mgesteiro/escornabot-Brivoi-DIY/3D/escornabot_back.png

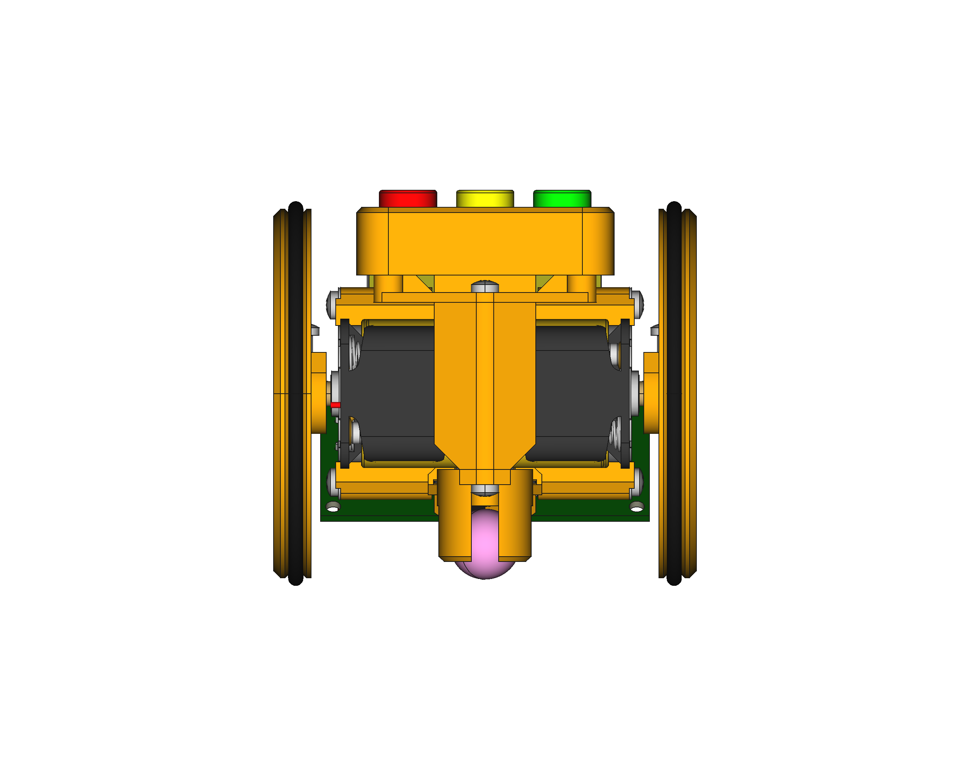
3D/escornabot_back.png
