mgesteiro/escornabot-Brivoi-DIY/3D/escornabot_bottom.png

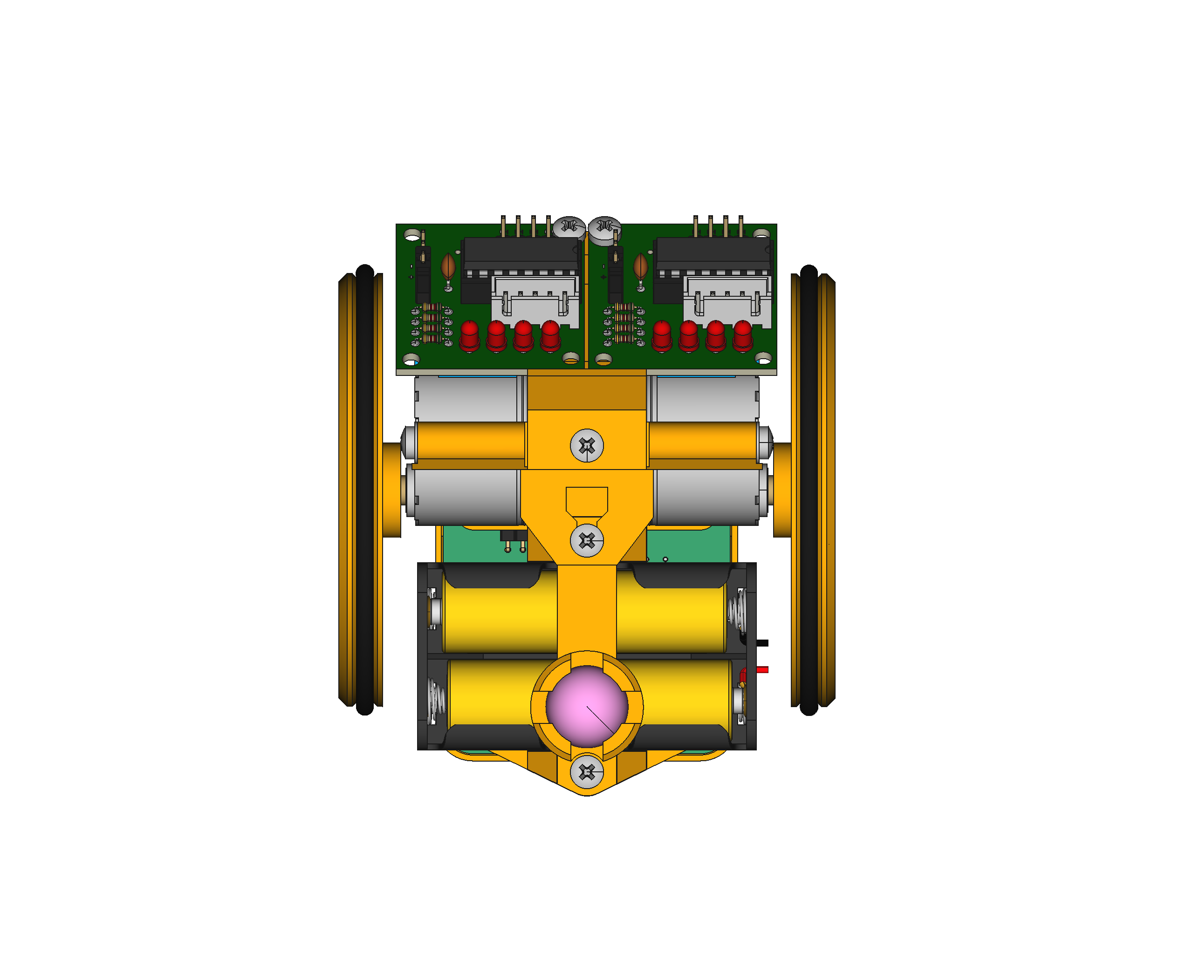
3D/escornabot_bottom.png
