mgesteiro/escornabot-Brivoi-DIY/3D/escornabot_front.png

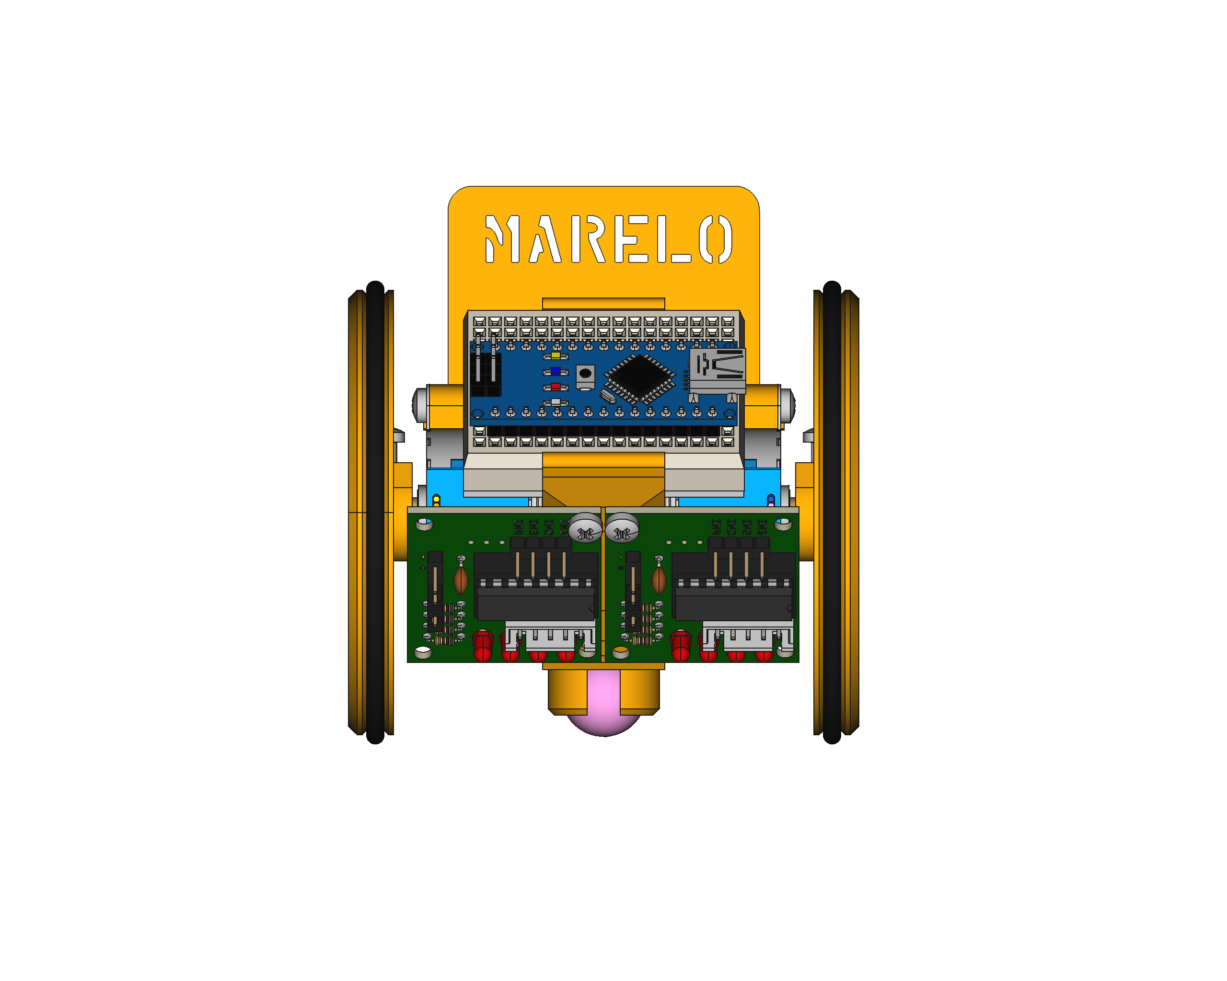
3D/escornabot_front.png
