mgesteiro/escornabot-Brivoi-DIY/3D/escornabot_left.png

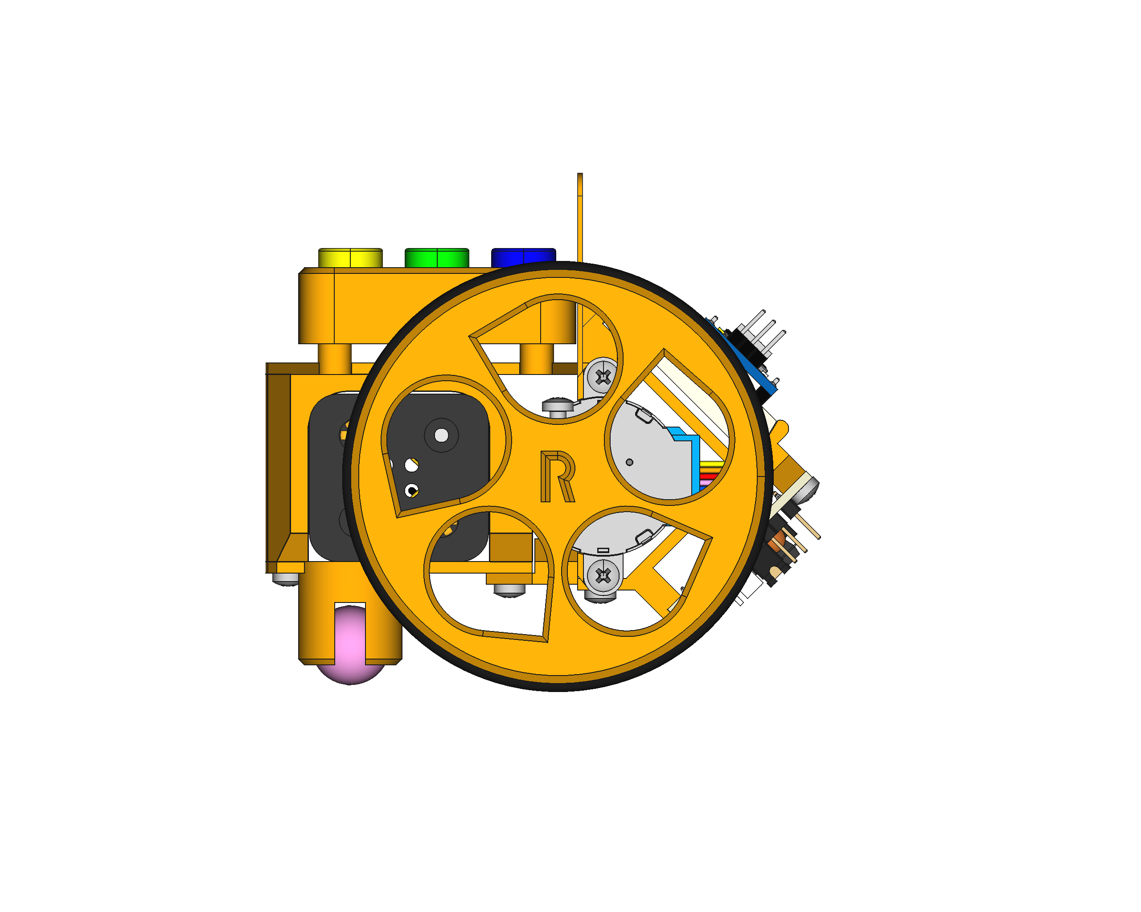
3D/escornabot_left.png
