mgesteiro/escornabot-Brivoi-DIY/3D/escornabot_right.png

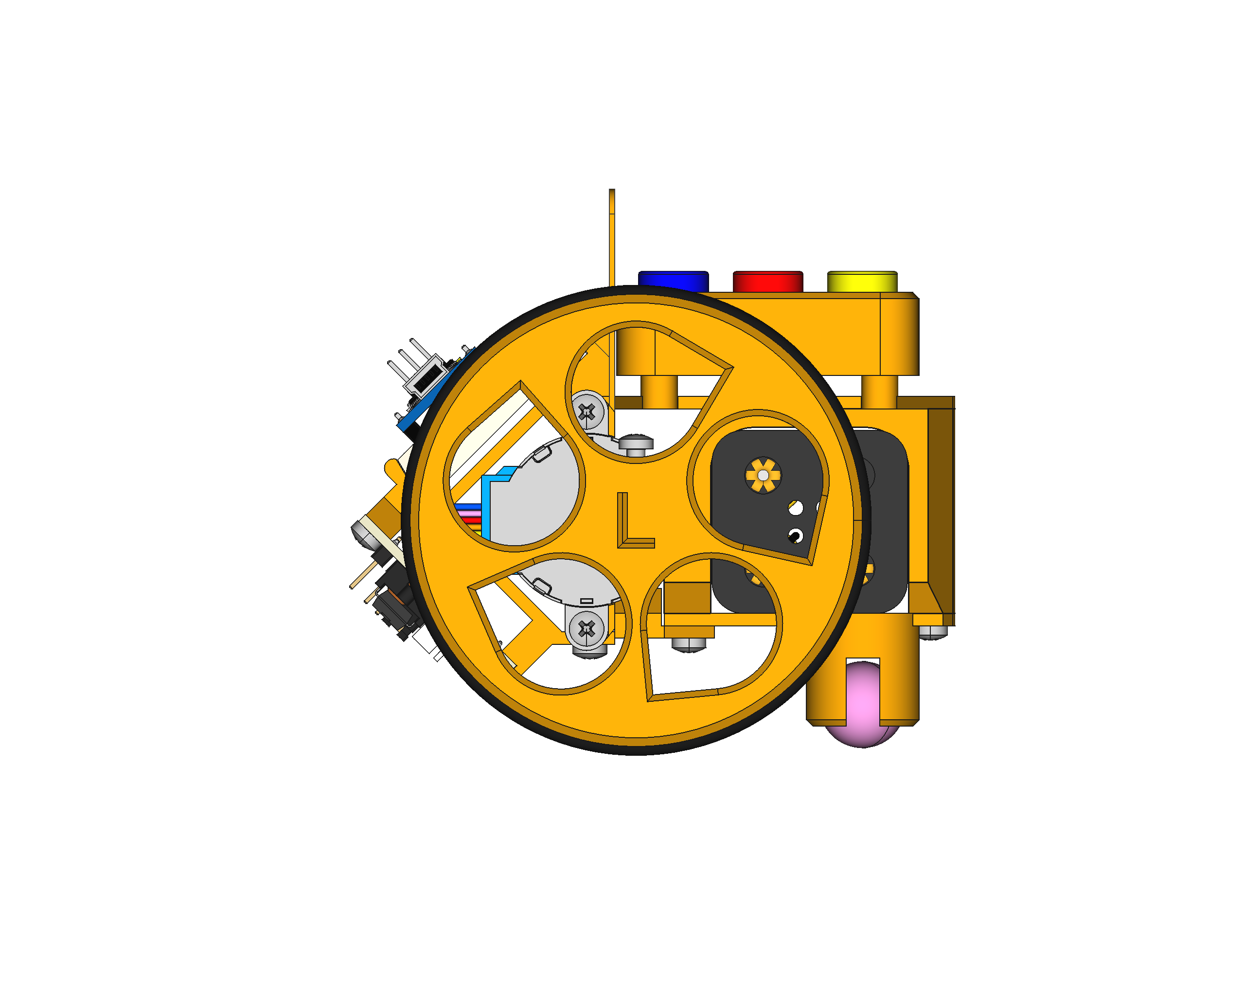
3D/escornabot_right.png
