mgesteiro/escornabot-Brivoi-DIY/3D/escornabot_top.png

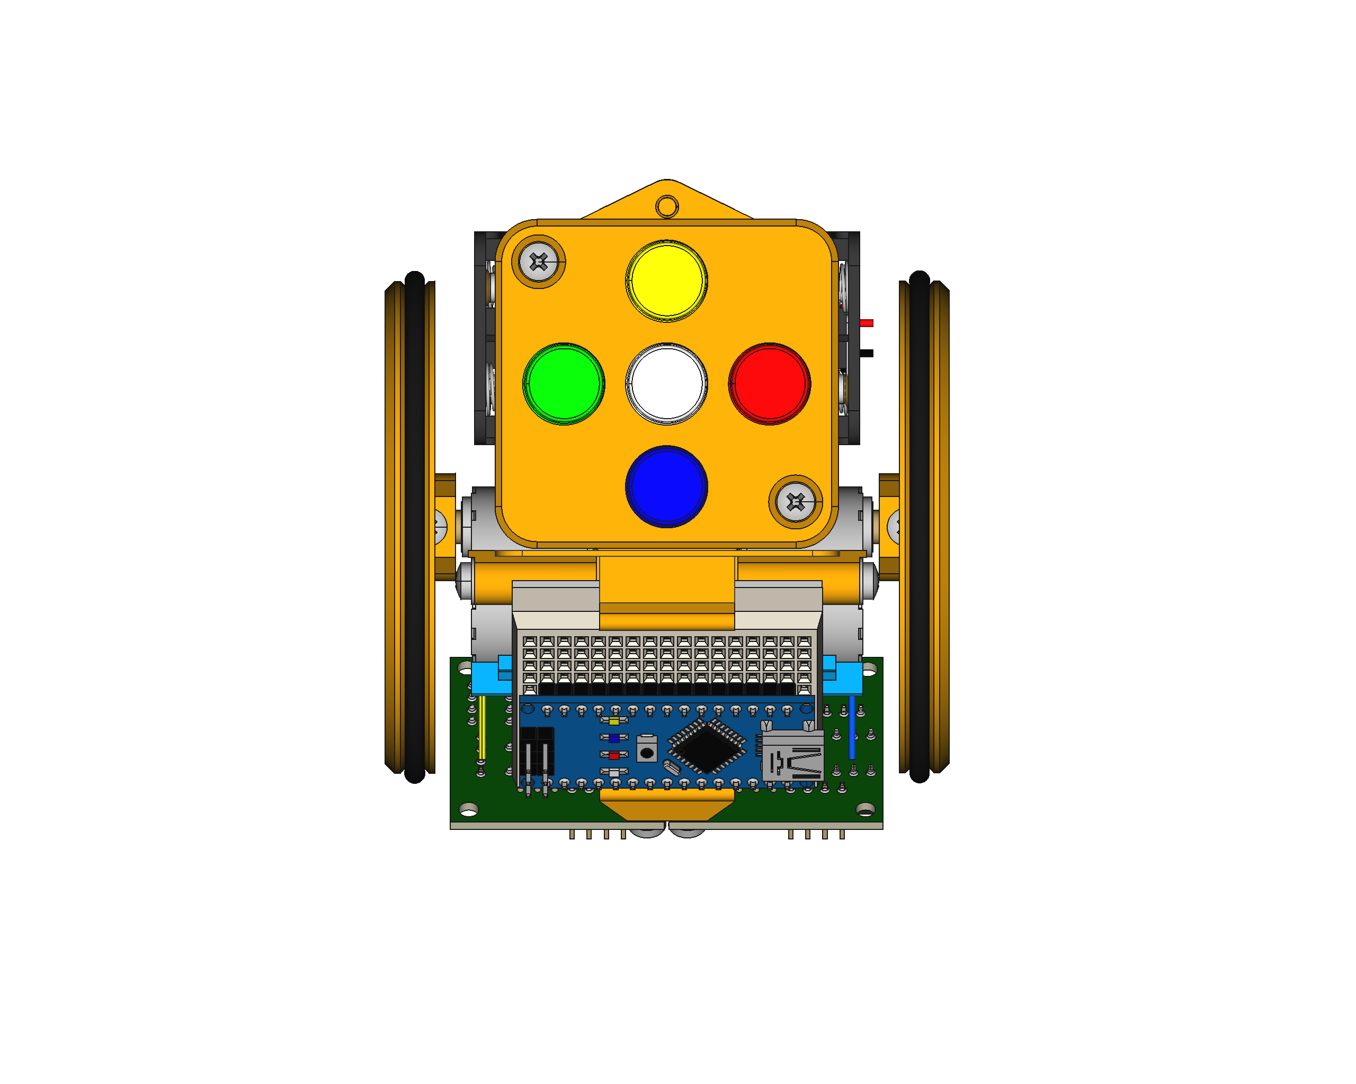
3D/escornabot_top.png
