mgesteiro/escornabot-Brivoi-DIY/3D/wheel-base.png

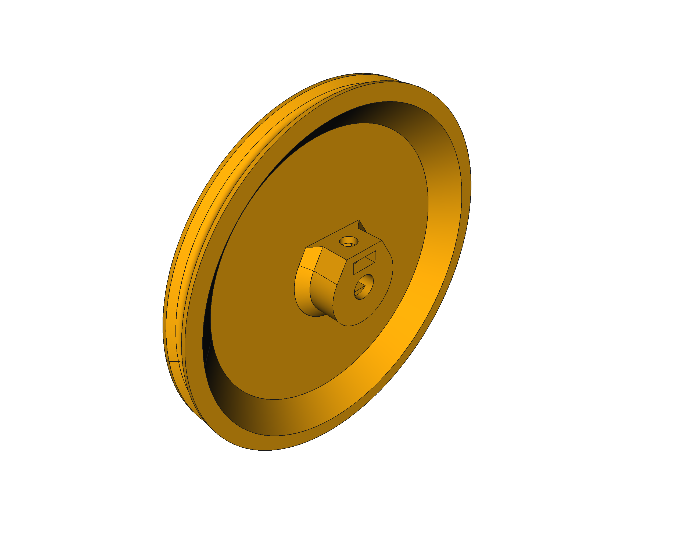
3D/wheel-base.png
