mgesteiro/escornabot-Brivoi-DIY/3D/battery-bracket-kit.FCStd

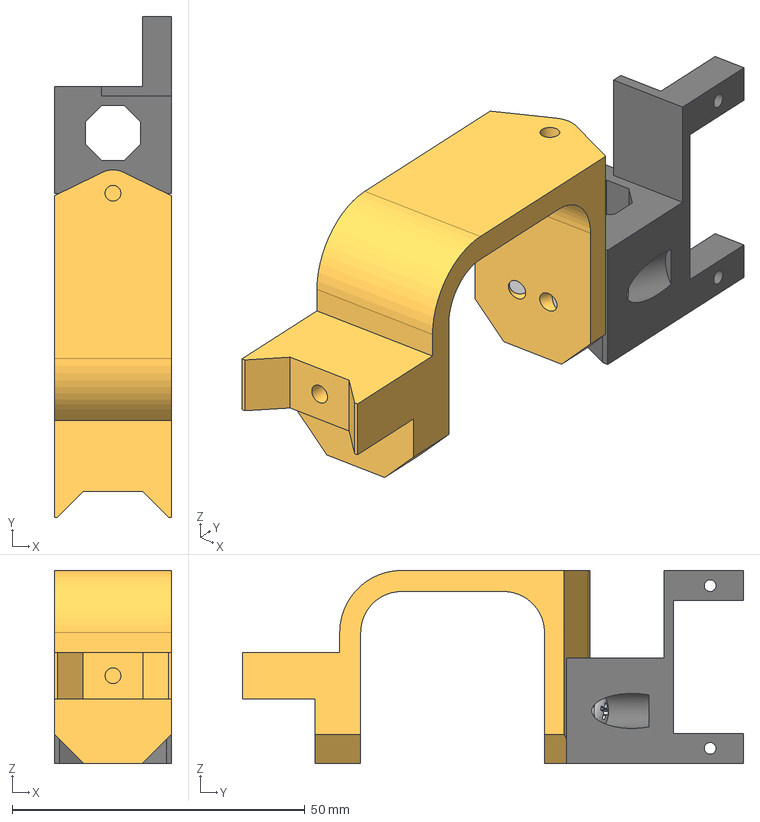
[picture p46: CAD file, 2022-03-19]
3D/battery-bracket-kit.FCStd
20.0 x 85.6 x 33.0 mm
Body-battery-bracket
M3x8-Screw-main-body01 x 2
M3x8-Screw-main-body02 x 2
kit-pintor x 2
