mgesteiro/escornabot-Brivoi-DIY/3D/switch-holder.FCStd

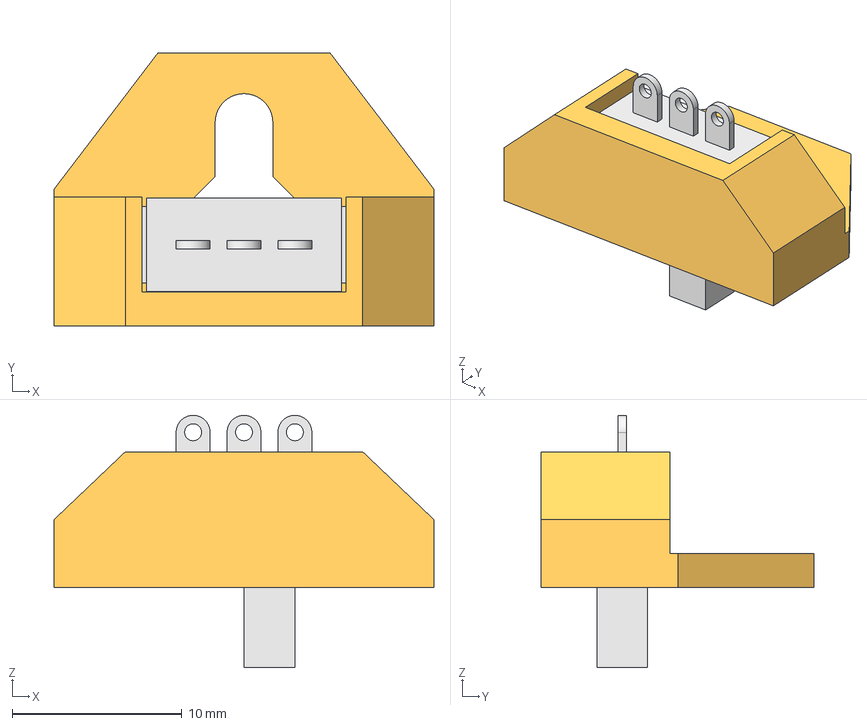
[picture p47: CAD file, 2022-03-12]
3D/switch-holder.FCStd
22.4 x 16.1 x 14.9 mm
Body-switch-holder
slide-switch
