mgesteiro/escornabot-Brivoi-DIY/3D/ball-caster.FCStd

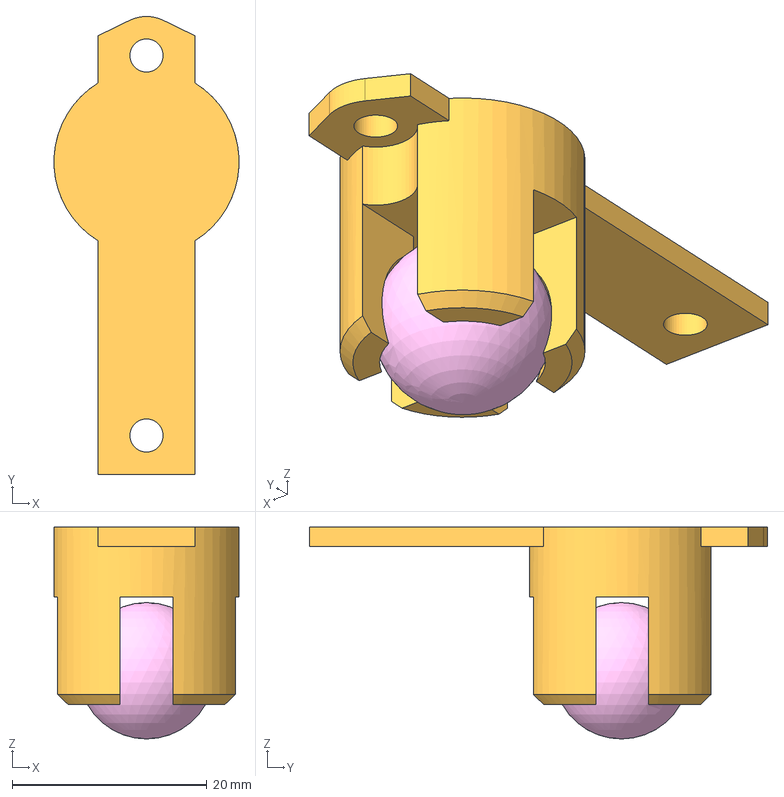
[picture p48: CAD file, 2022-03-12]
3D/ball-caster.FCStd
19.0 x 47.0 x 21.8 mm
Body-ball-caster
ball
