mgesteiro/escornabot-Brivoi-DIY/3D/keypad-cover.FCStd

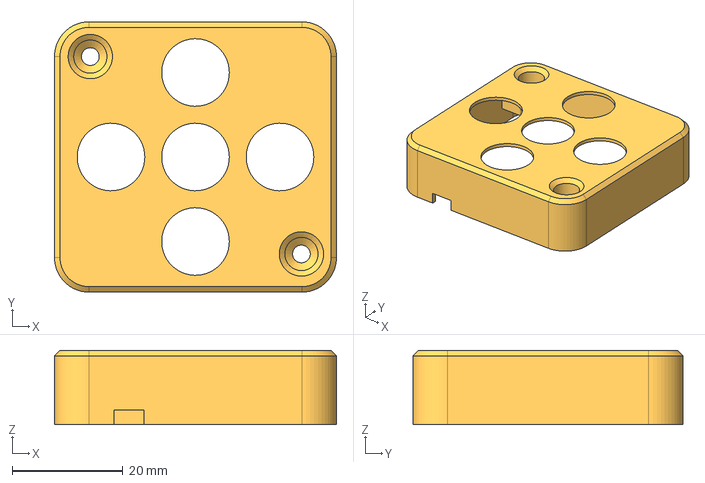
[picture p49: CAD file, 2021-10-16]
3D/keypad-cover.FCStd
50.9 x 48.8 x 13.4 mm
