mgesteiro/escornabot-Brivoi-DIY/3D/battery-bracket.FCStd

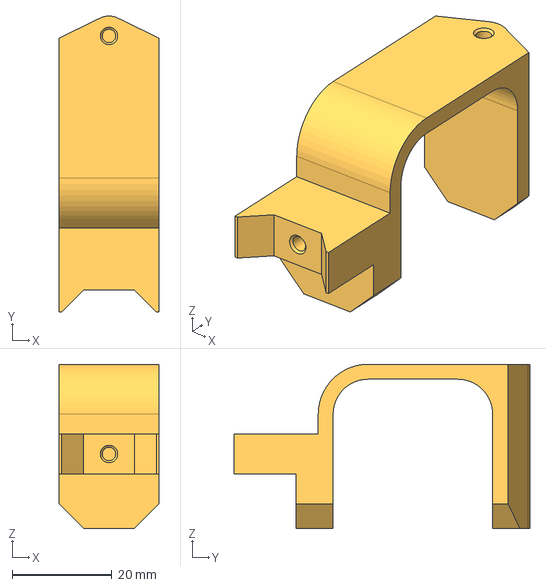
[picture p50: CAD file, 2021-10-16]
3D/battery-bracket.FCStd
20.0 x 59.4 x 33.0 mm
