mgesteiro/escornabot-Brivoi-DIY/3D/motor-bracket.FCStd

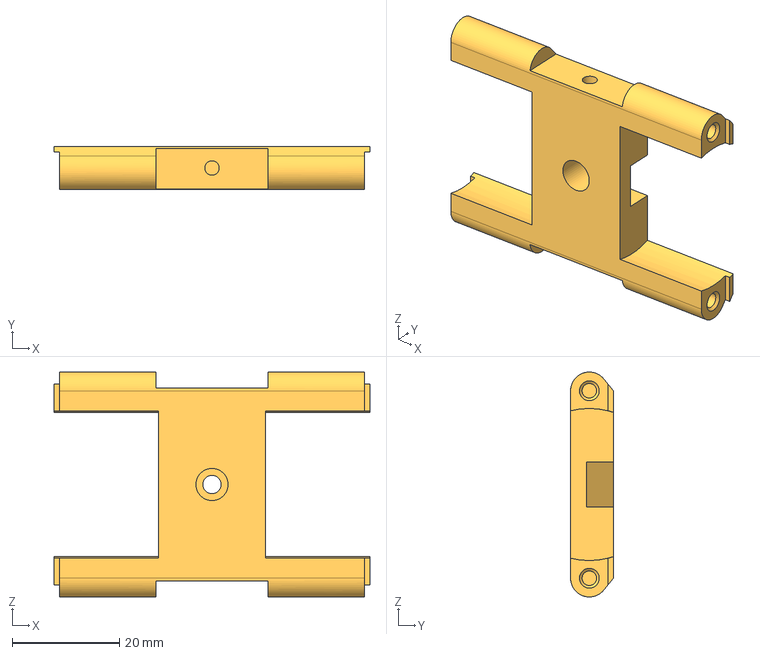
[picture p51: CAD file, 2021-10-16]
3D/motor-bracket.FCStd
59.0 x 8.00 x 42.0 mm
