mgesteiro/escornabot-Brivoi-DIY/3D/escornaface.FCStd

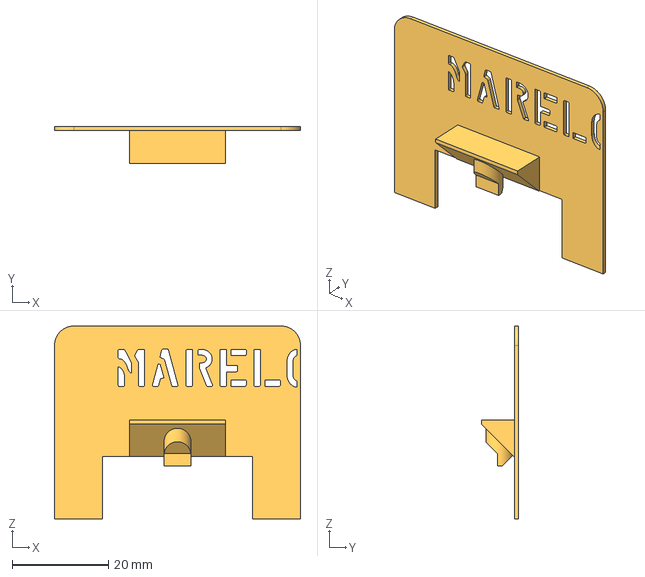
[picture p52: CAD file, 2021-10-16]
3D/escornaface.FCStd
51.0 x 7.70 x 40.0 mm
