mgesteiro/escornabot-Brivoi-DIY/3D/ogaki-cpu-holder.FCStd

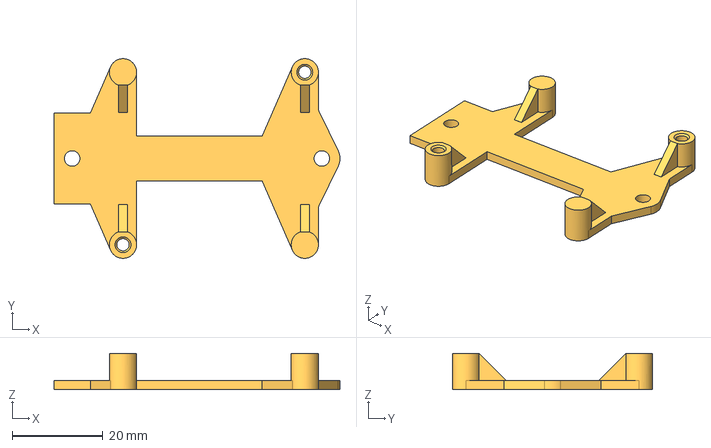
[picture p53: CAD file, 2021-06-24]
3D/ogaki-cpu-holder.FCStd
63.0 x 44.0 x 8.00 mm
