mgesteiro/escornabot-Brivoi-DIY/3D/keypad-cover-sq.FCStd

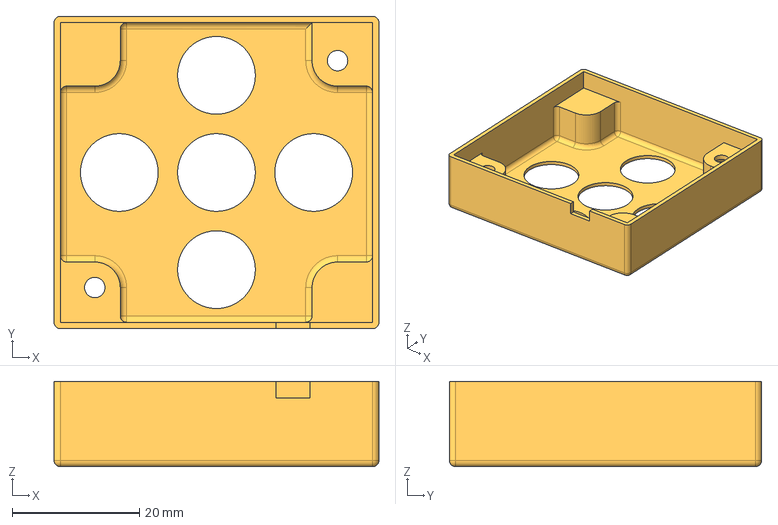
[picture p54: CAD file, 2020-04-19]
3D/keypad-cover-sq.FCStd
51.0 x 49.0 x 13.4 mm
